fehgab/AXON-UPS/Software/include/currentdt.h

// Current time: Tue Mar 09 20:02:07 2010  by ZBI 2007. 

#define CURRENTTIME 200207
#define CURRENTDATE 20100309

#define RND_MNUMB_0 0x2F510CD1
#define RND_MNUMB_1 0x38337C92
#define RND_MNUMB_2 0x73BE6D08
#define RND_MNUMB_3 0xA7451A1
