fehgab/AXON-UPS/Software/include/bbx_vars.h

/* bbx */
extern unsigned int* bbx_val1_addr;
extern unsigned int* bbx_val2_addr;
extern unsigned int* bbx_val3_addr;
extern unsigned int* bbx_val4_addr;
extern int bbx_trigger_ch;
extern int bbx_trig_level;
extern int bbx_trig_delay;
extern int bbx_trig_ch_val_old;
extern int bbx_trig_ch_val;
extern int bbx_trig_slope;
extern unsigned int bbx_pretrigger;
extern int	bbx_state;
extern unsigned int  bbx_end_idx;
extern unsigned int  bbx_start_idx;
extern unsigned int  bbx_idx;
extern unsigned int  bbx_sample_time;
extern unsigned int  bbx_div;

extern void bbx_trigger();
extern void bbx_inic();
