fehgab/AXON-UPS/Software/include/gen_types.h

#ifndef _BF537_TYPES_H_
#define _BF537_TYPES_H_

typedef char               int8_t;
typedef unsigned char      uint8_t;
typedef int                int16_t;
typedef unsigned int       uint16_t;
typedef long               int32_t;
typedef unsigned long      uint32_t;


#endif
